Koveto/RPNCalculator/program/config.py

"""
config.py
Kobe Goodwin
4/30/2025

Global variables relating to calculator
"""

button_mode = False
orient_top_bottom = False
degrees = True
polar = False
hexadecimal = False
scientific = False
storing = False
recalling = False
